sasha-nordiclab/ROTEK-A01VP/references/photos/IMG_7259.jpg

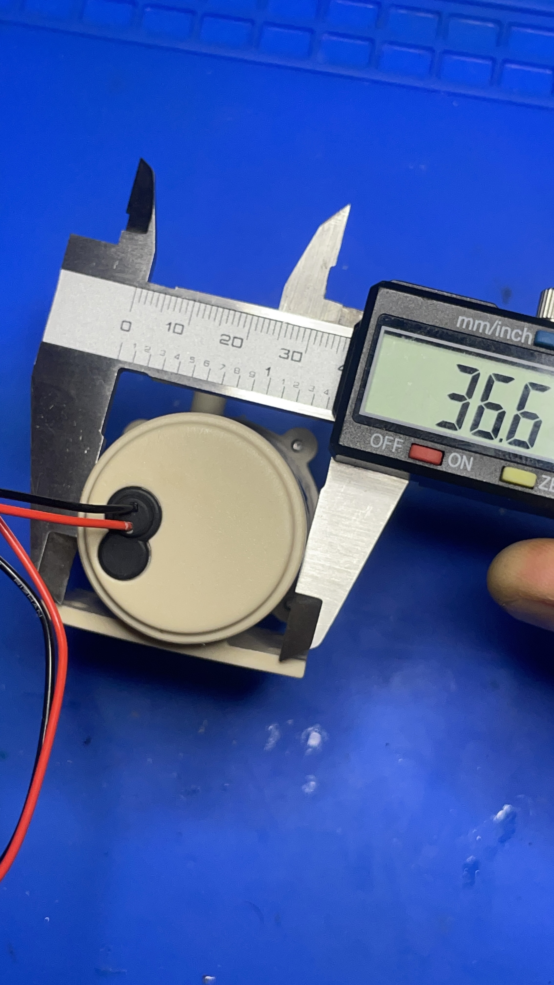
references/photos/IMG_7259.jpg
