sasha-nordiclab/ROTEK-A01VP/references/photos/IMG_7271.JPG

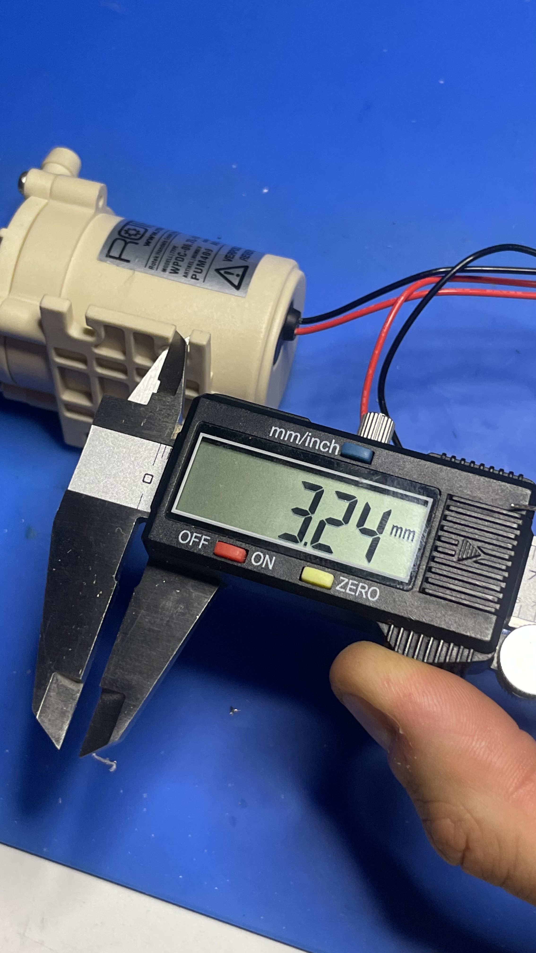
references/photos/IMG_7271.JPG
