sasha-nordiclab/ROTEK-A01VP/references/photos/IMG_7273.JPG

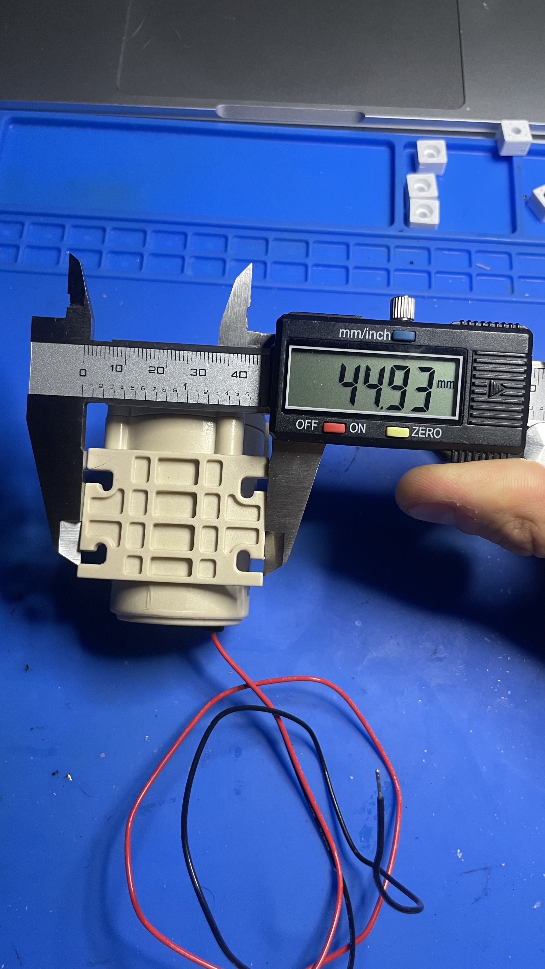
references/photos/IMG_7273.JPG
