sasha-nordiclab/ROTEK-A01VP/references/photos/IMG_7274.JPG

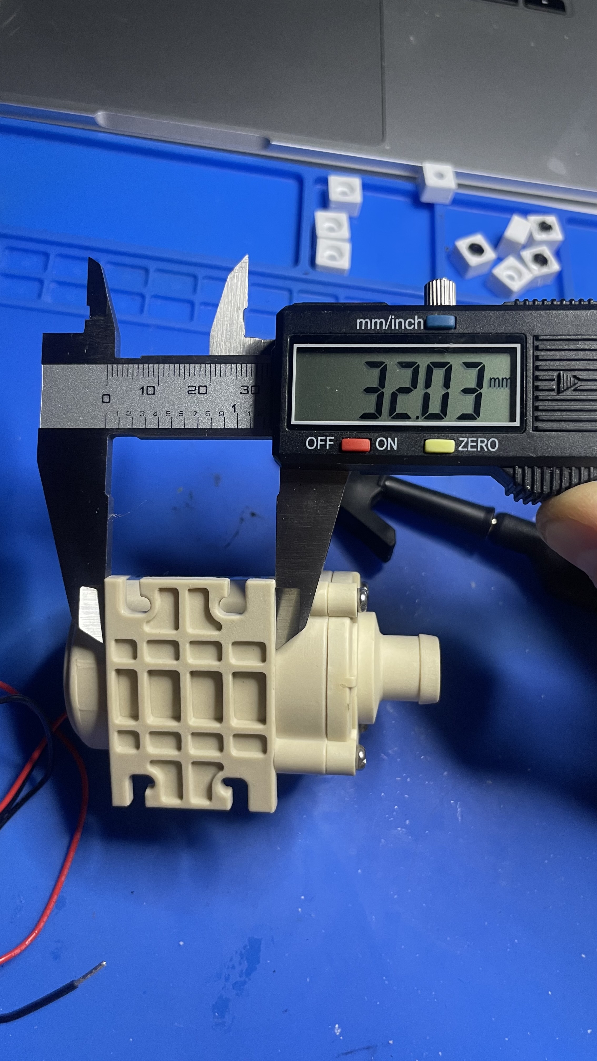
references/photos/IMG_7274.JPG
