sasha-nordiclab/ROTEK-A01VP/references/photos/IMG_7276.JPG

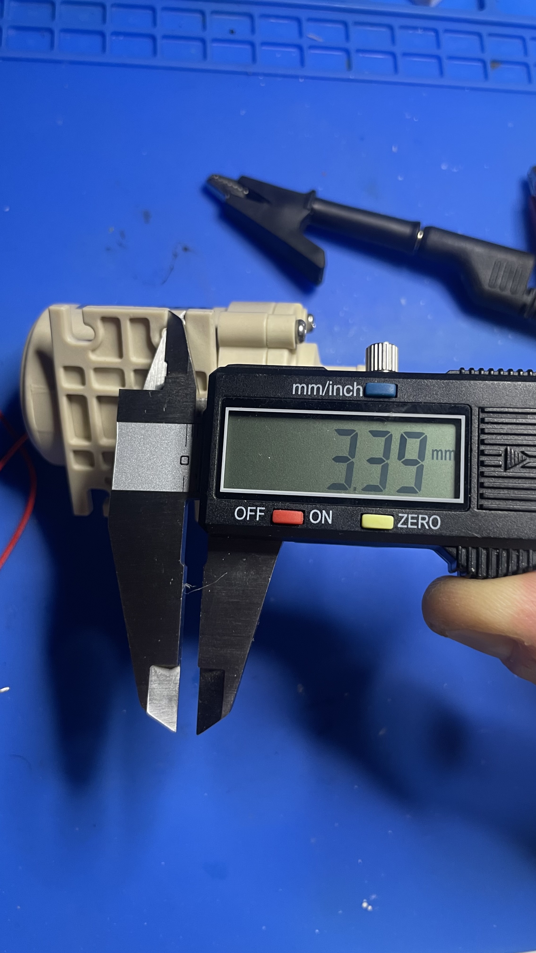
references/photos/IMG_7276.JPG
