sasha-nordiclab/ROTEK-A01VP/references/photos/IMG_7277.JPG

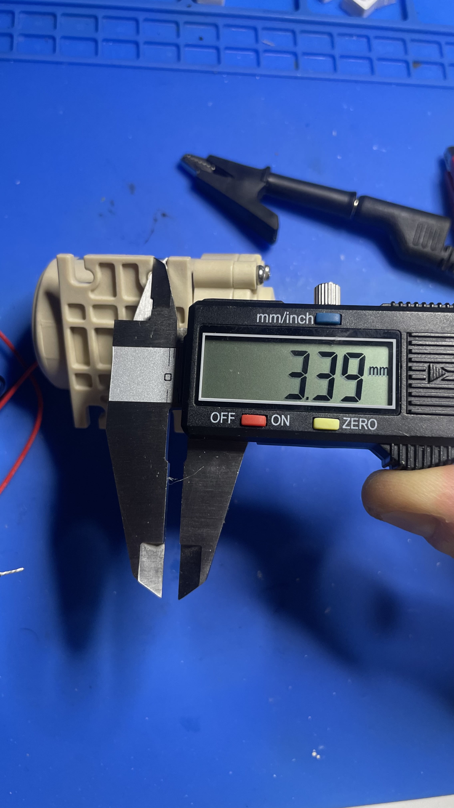
references/photos/IMG_7277.JPG
