sasha-nordiclab/ROTEK-A01VP/references/photos/IMG_7278.JPG

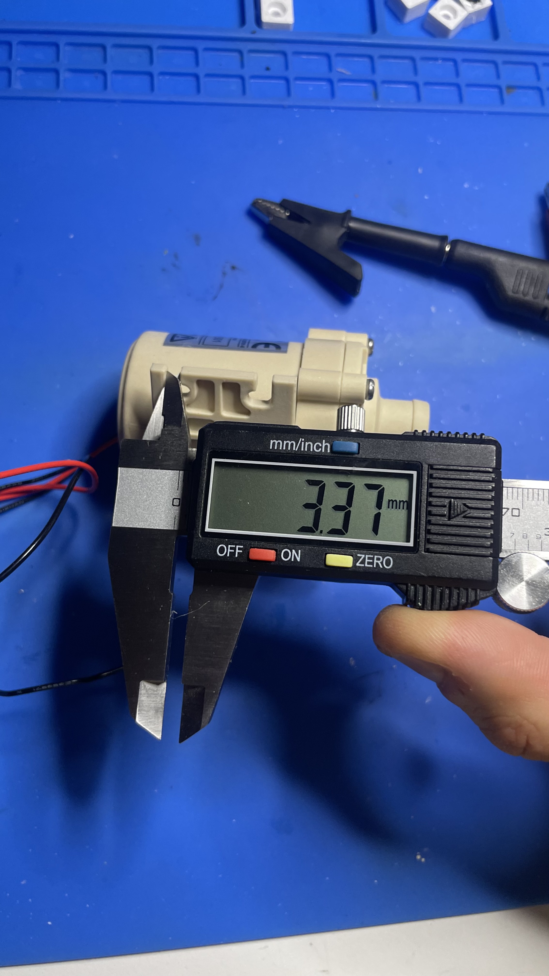
references/photos/IMG_7278.JPG
