sasha-nordiclab/ROTEK-A01VP/references/photos/IMG_7279.JPG

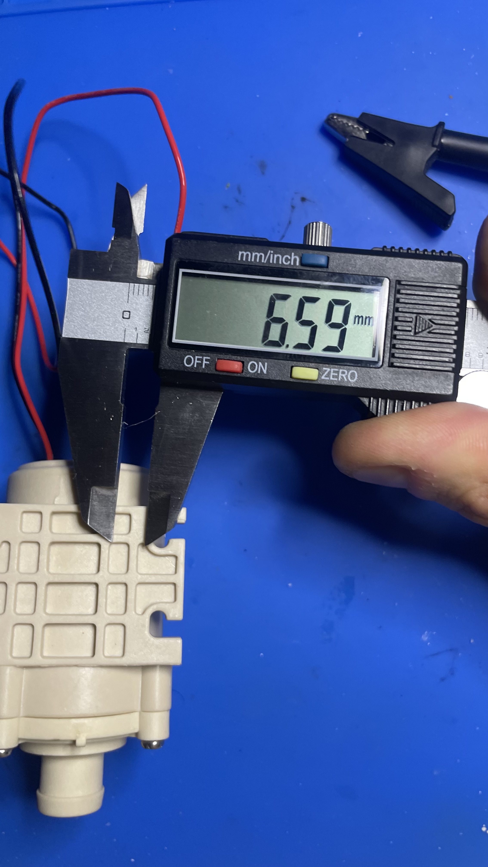
references/photos/IMG_7279.JPG
