sasha-nordiclab/ROTEK-A01VP/references/photos/IMG_7280.JPG

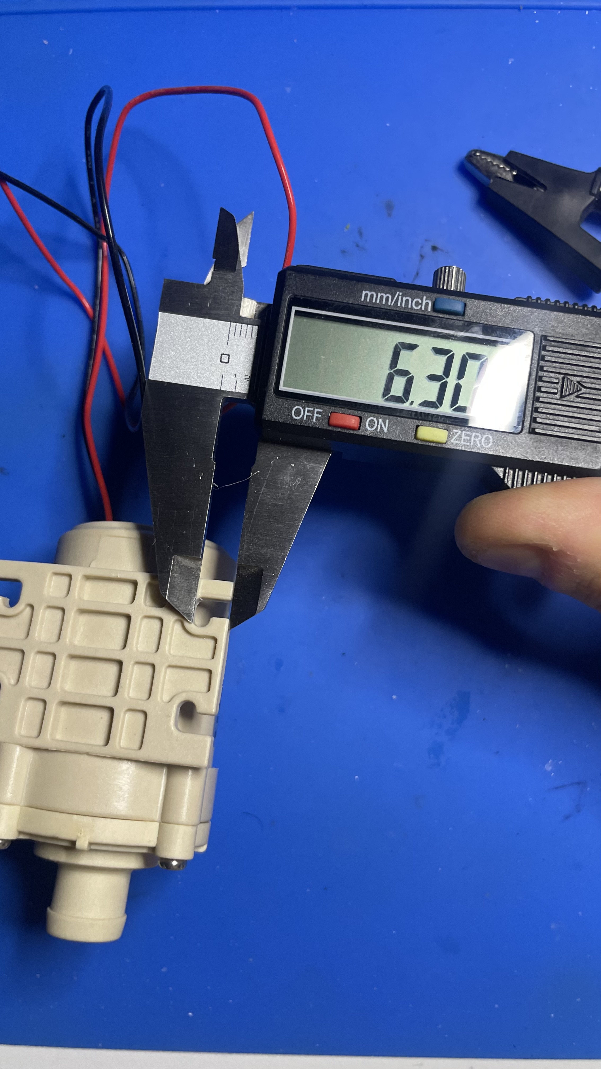
references/photos/IMG_7280.JPG
