sasha-nordiclab/ROTEK-A01VP/references/photos/IMG_7281.JPG

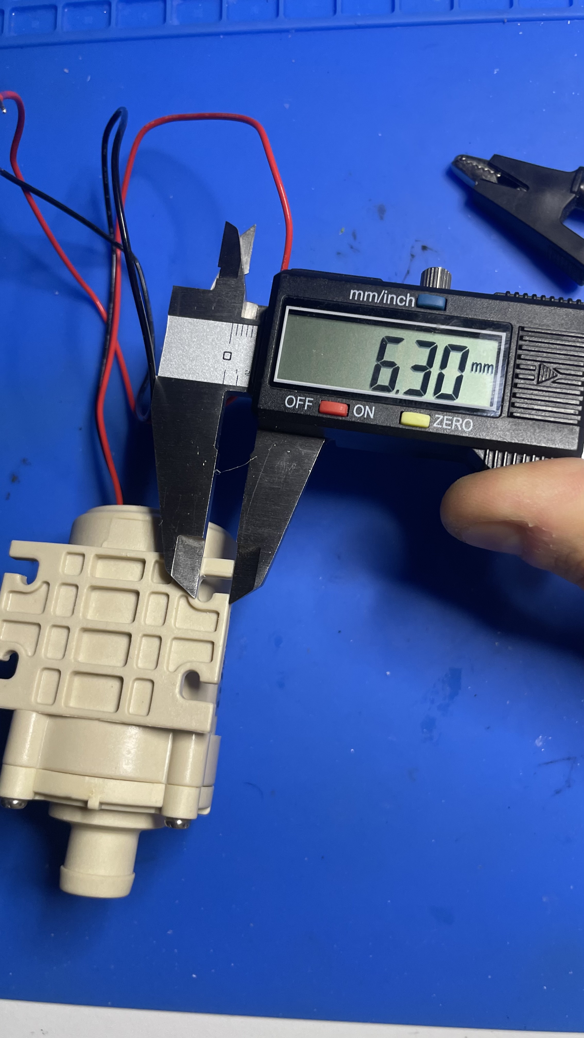
references/photos/IMG_7281.JPG
