sasha-nordiclab/ROTEK-A01VP/references/photos/IMG_7283.JPG

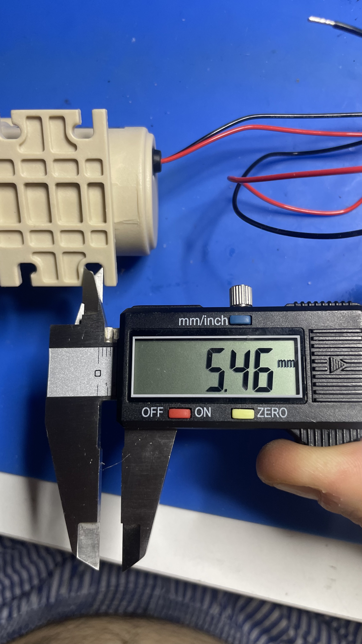
references/photos/IMG_7283.JPG
