sasha-nordiclab/ROTEK-A01VP/references/photos/IMG_7285.JPG

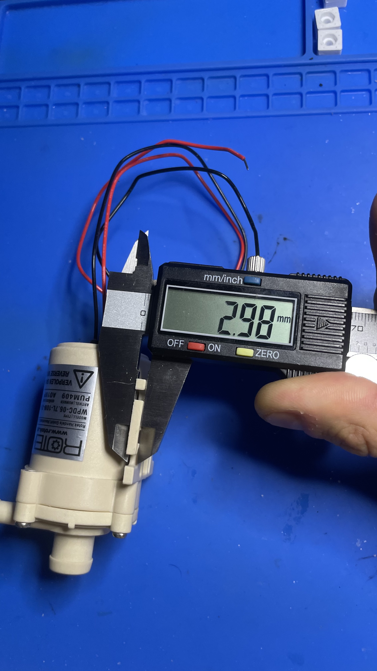
references/photos/IMG_7285.JPG
