sasha-nordiclab/ROTEK-A01VP/references/photos/IMG_7286.JPG

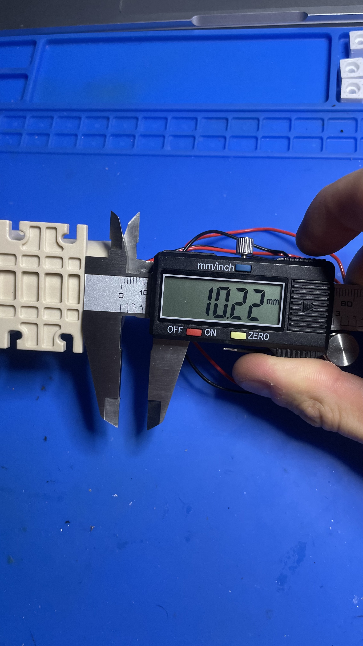
references/photos/IMG_7286.JPG
