sasha-nordiclab/ROTEK-A01VP/references/photos/IMG_7293.jpeg

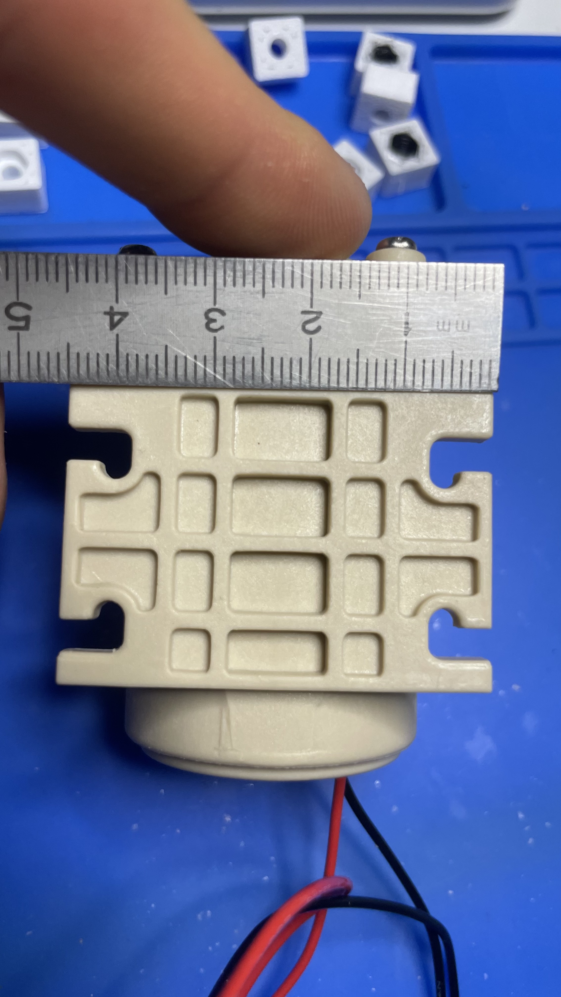
references/photos/IMG_7293.jpeg
