sasha-nordiclab/ROTEK-A01VP/references/photos/IMG_7294.JPG

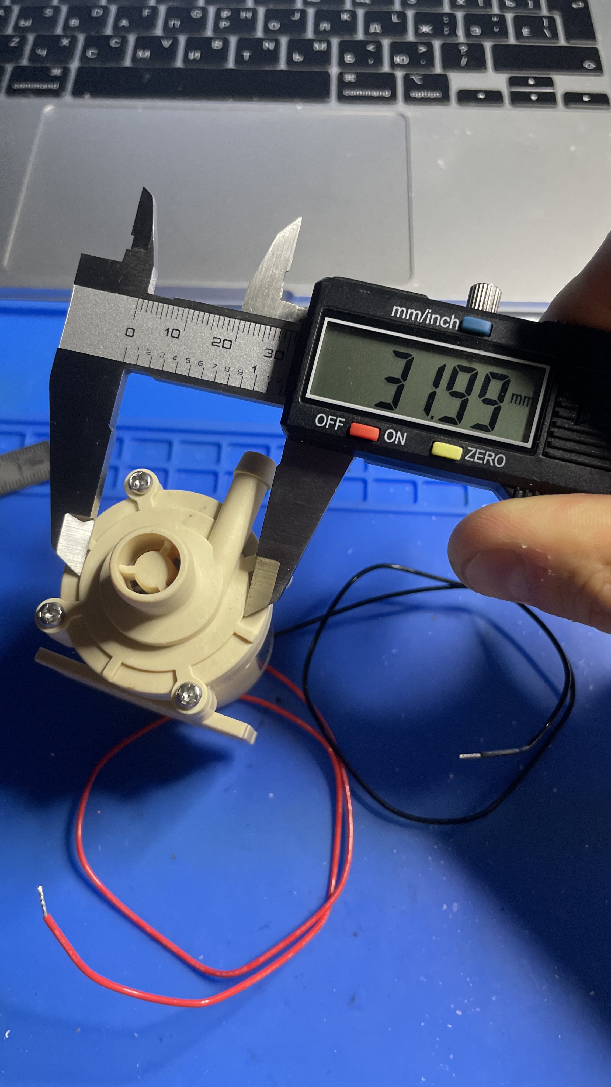
references/photos/IMG_7294.JPG
