sasha-nordiclab/ROTEK-A01VP/references/photos/IMG_7295.JPG

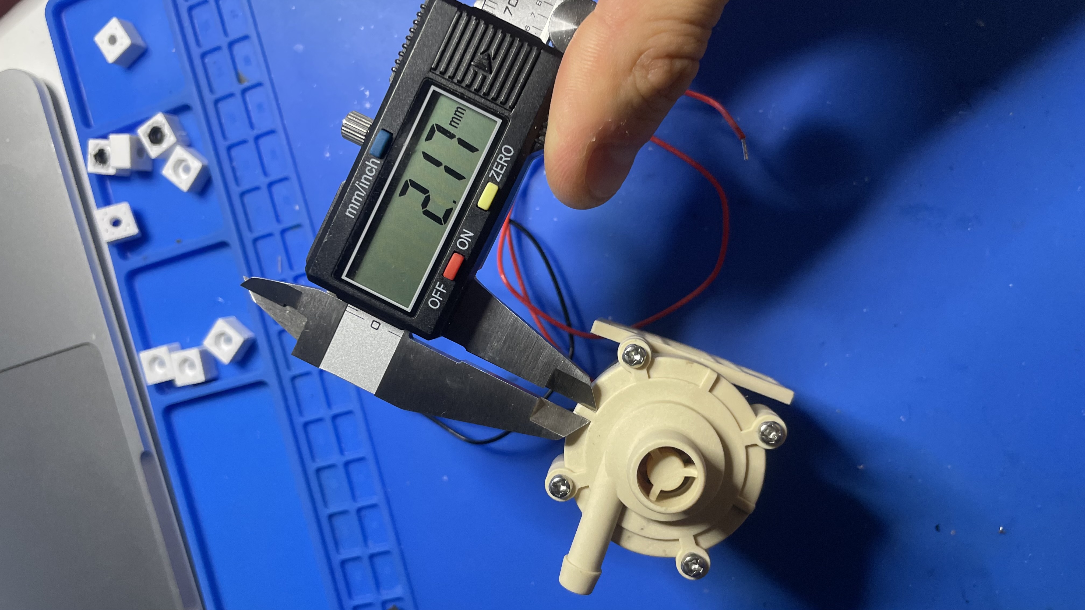
references/photos/IMG_7295.JPG
