sasha-nordiclab/ROTEK-A01VP/references/photos/IMG_7296.jpeg

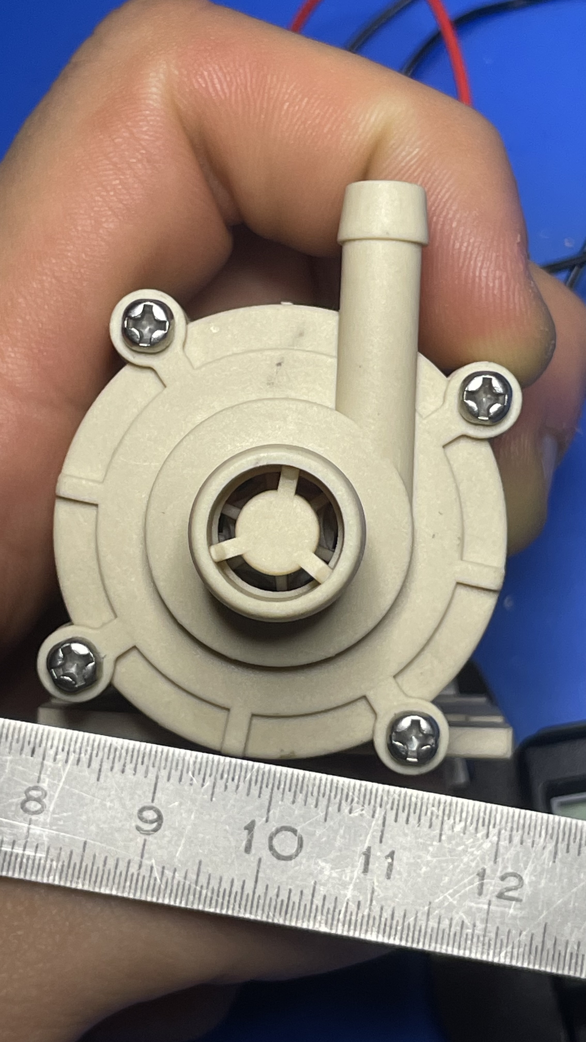
references/photos/IMG_7296.jpeg
