sasha-nordiclab/ROTEK-A01VP/references/pump_drawing.jpg

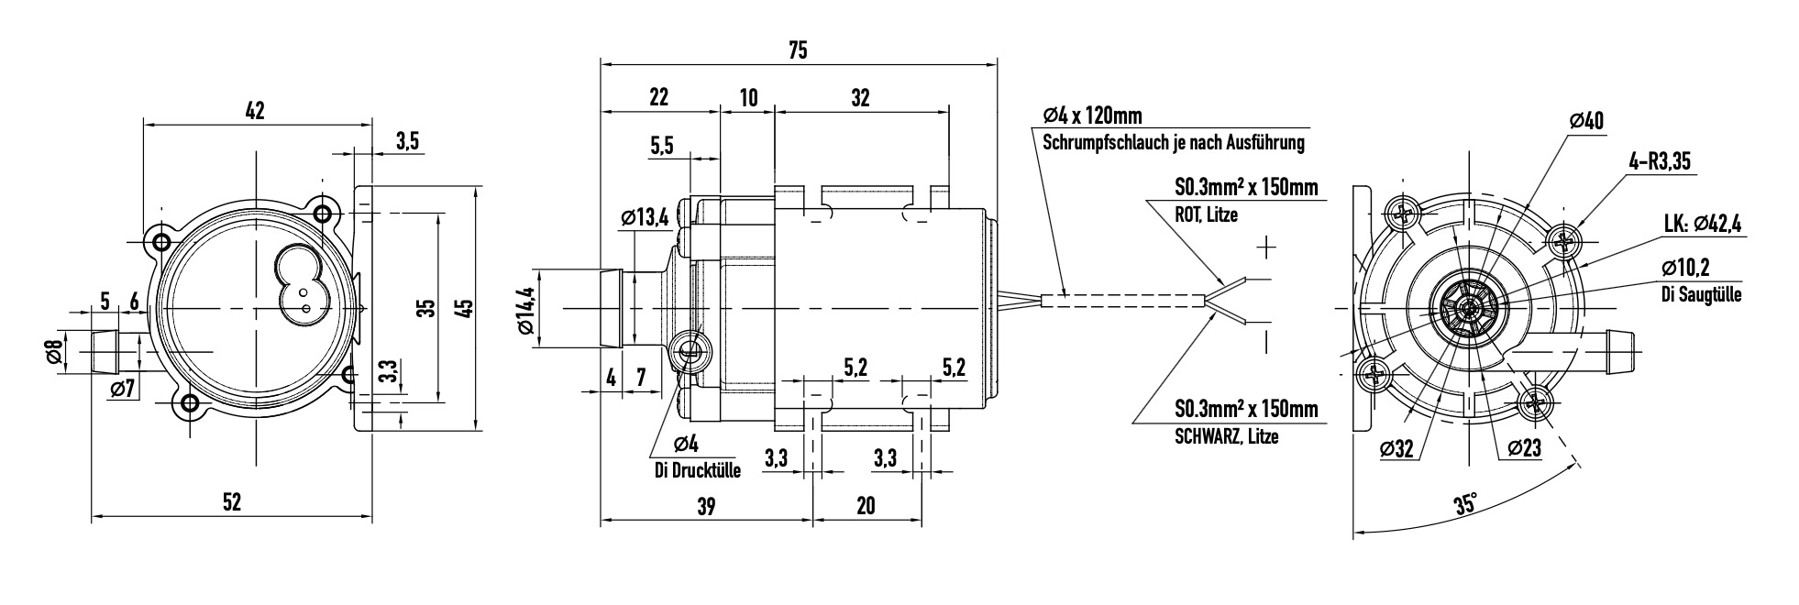
references/pump_drawing.jpg
